tobst/radmesserS/images/device/device_case_2.jpg

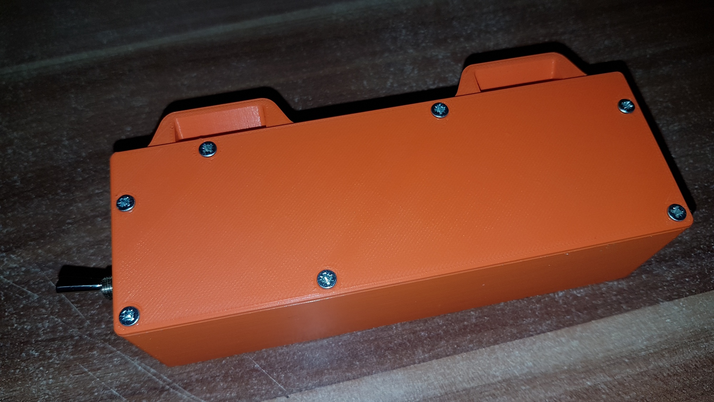
images/device/device_case_2.jpg
