tobst/radmesserS/images/device/device_case_3.jpg

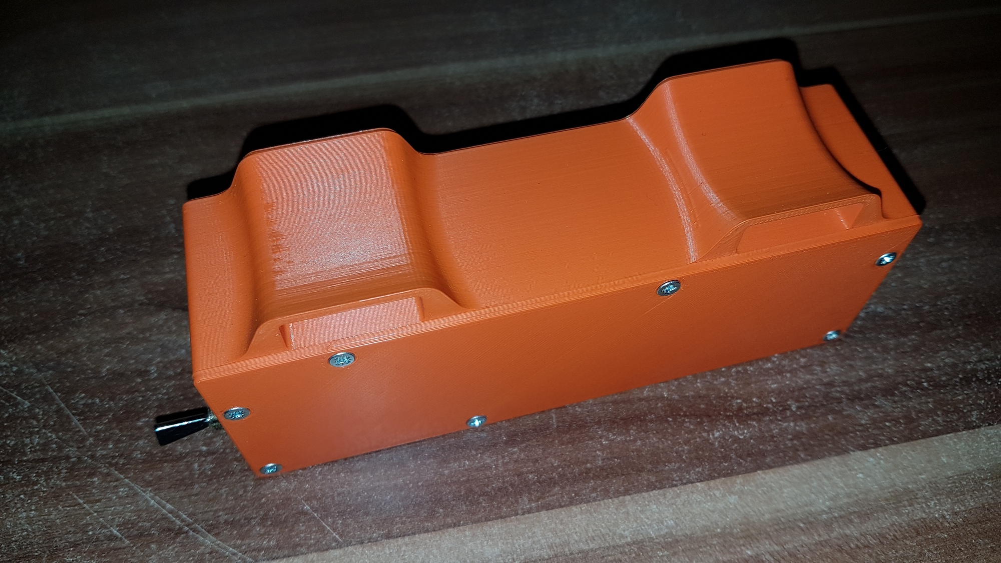
images/device/device_case_3.jpg
