tobst/radmesserS/images/device/device_case_4.jpg

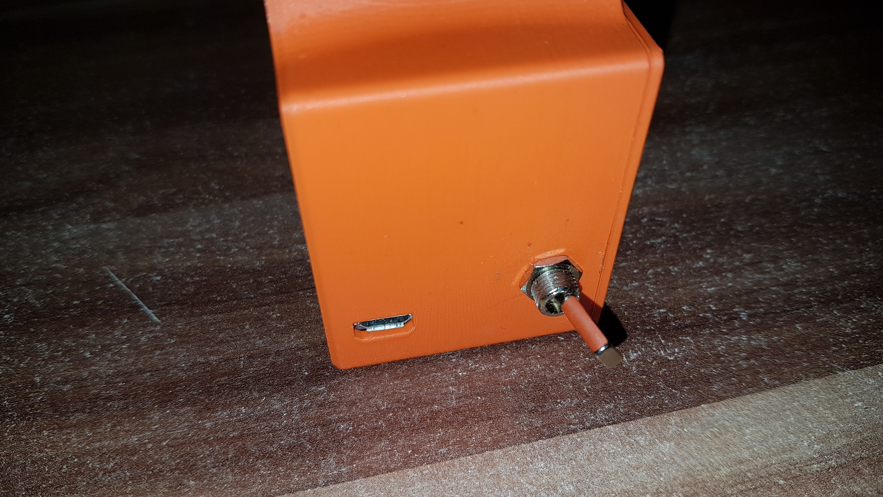
images/device/device_case_4.jpg
