tobst/radmesserS/images/device/device_internals.jpg

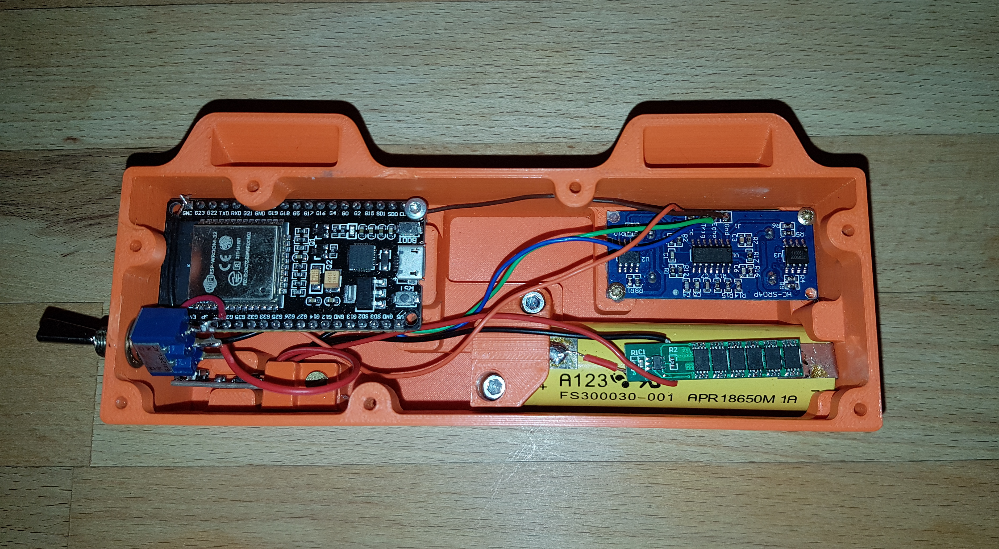
images/device/device_internals.jpg
