tobst/radmesserS/images/device/radmessers-fritzing.png

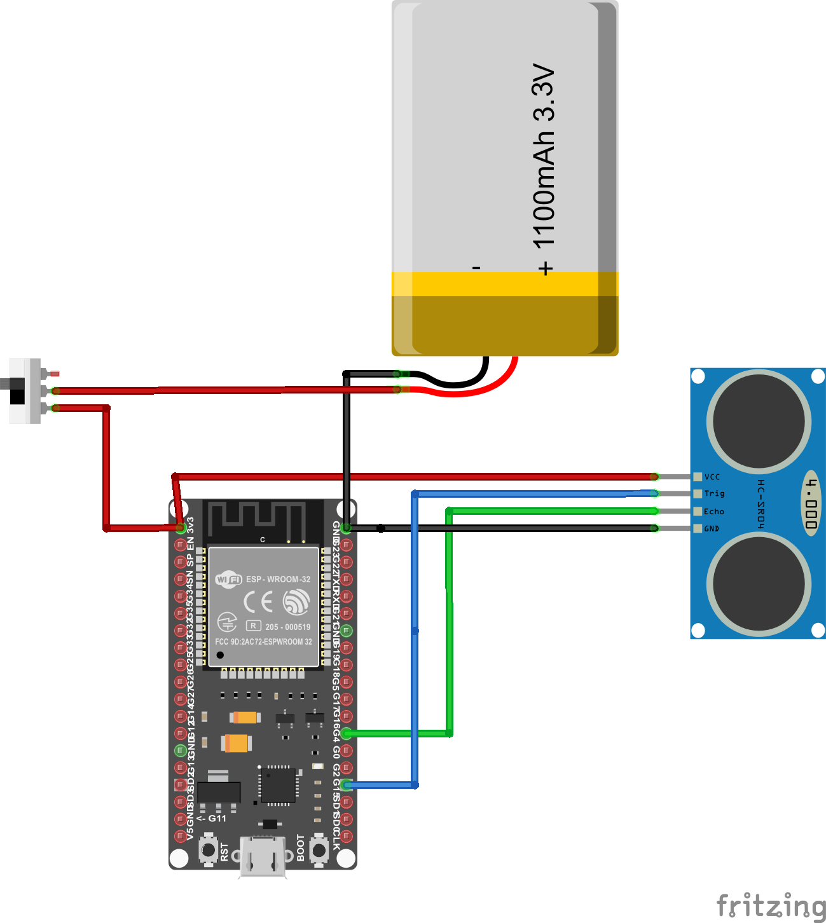
images/device/radmessers-fritzing.png
