tobst/radmesserS/images/device/TP5000-Charger-and-LiFePo-Protection-Board.jpg

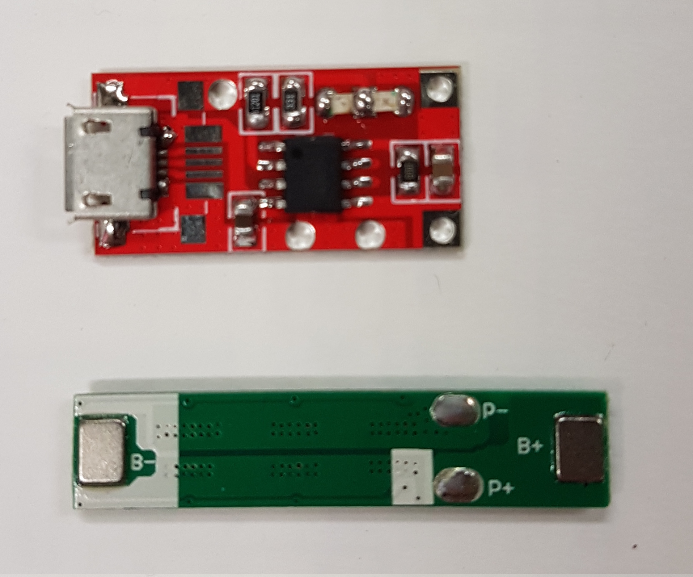
images/device/TP5000-Charger-and-LiFePo-Protection-Board.jpg
