tobst/radmesserS/images/mounting_0.jpg

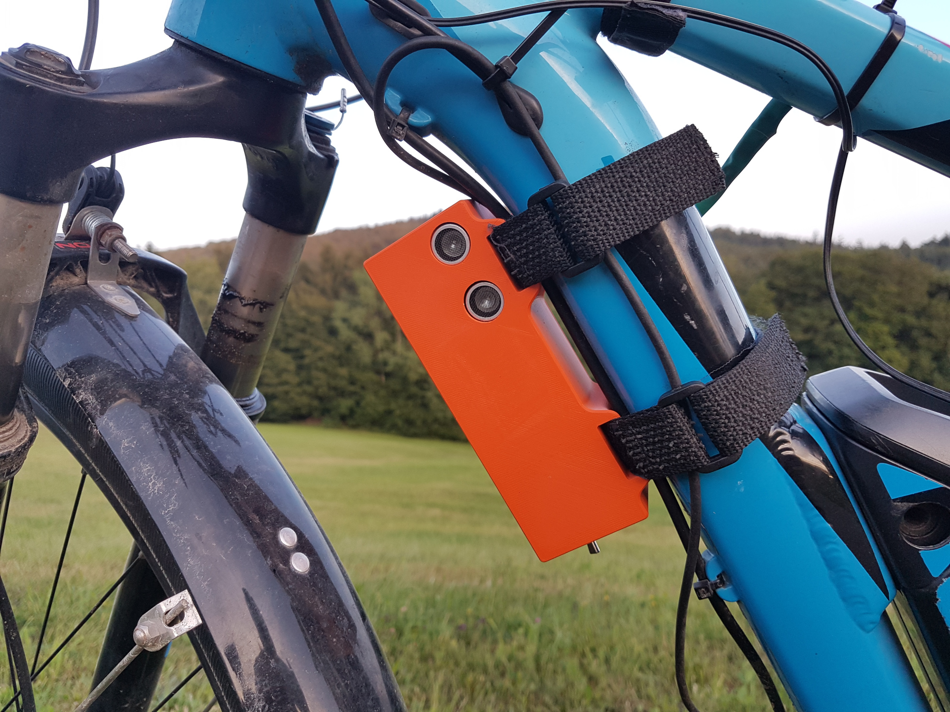
images/mounting_0.jpg
