tobst/radmesserS/images/screenshots/blescanner/ble_scanner_1.jpg

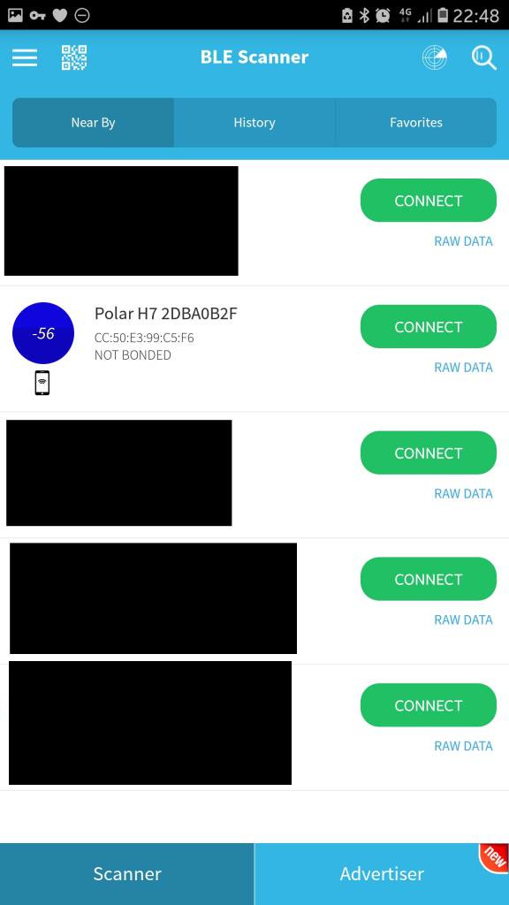
images/screenshots/blescanner/ble_scanner_1.jpg
