tobst/radmesserS/images/screenshots/blescanner/ble_scanner_2.jpg

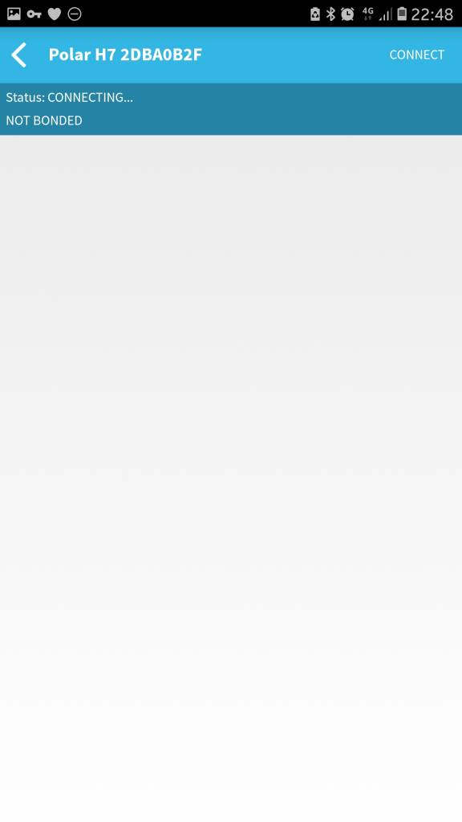
images/screenshots/blescanner/ble_scanner_2.jpg
