tobst/radmesserS/images/screenshots/blescanner/ble_scanner_2_800x800.jpg

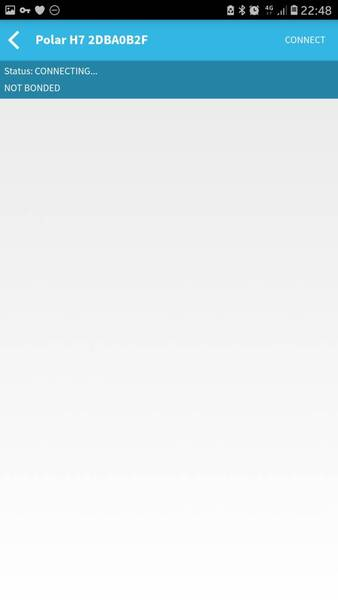
images/screenshots/blescanner/ble_scanner_2_800x800.jpg
