tobst/radmesserS/images/screenshots/blescanner/ble_scanner_3.jpg

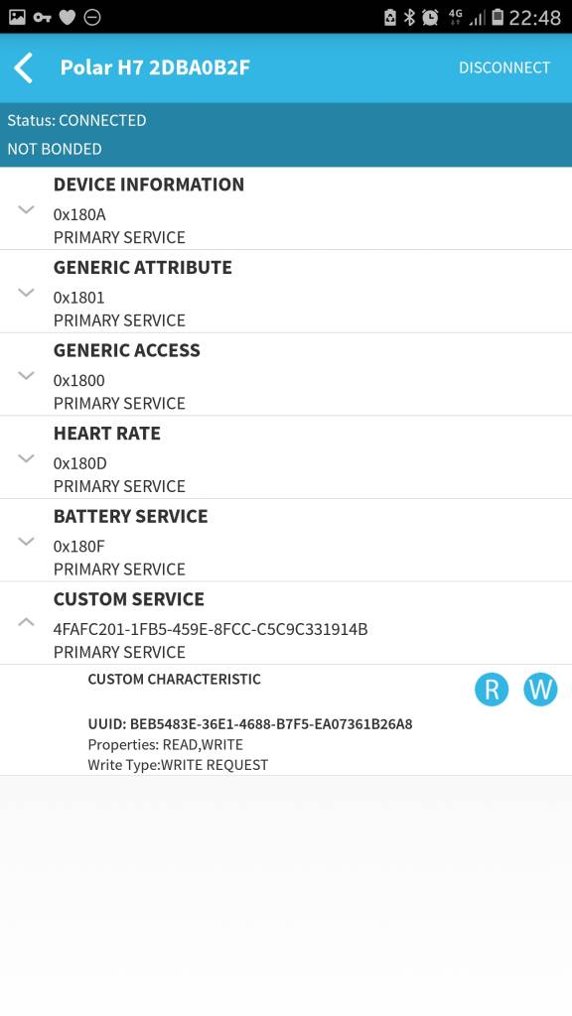
images/screenshots/blescanner/ble_scanner_3.jpg
