tobst/radmesserS/images/screenshots/blescanner/ble_scanner_4.jpg

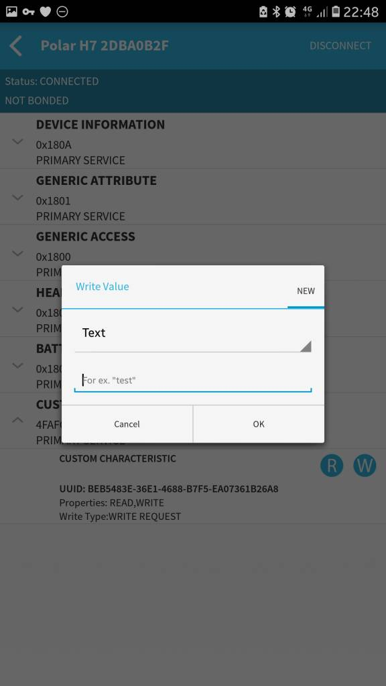
images/screenshots/blescanner/ble_scanner_4.jpg
