tobst/radmesserS/images/screenshots/runnerup/export/runnerup_export_to_directory_1.jpg

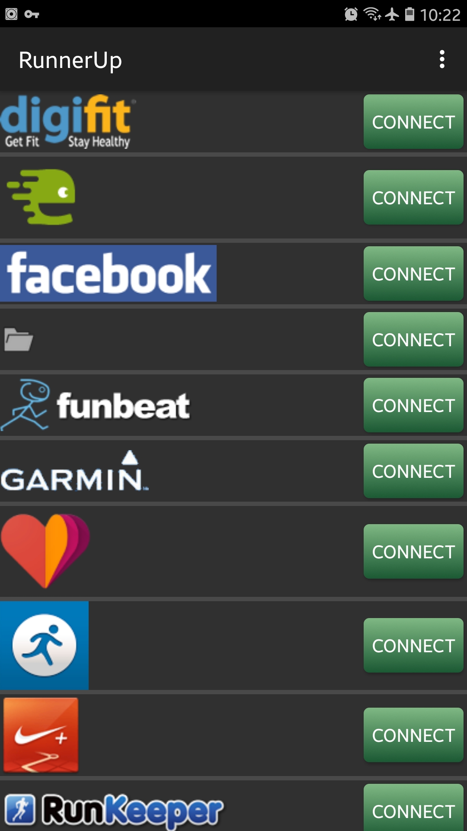
images/screenshots/runnerup/export/runnerup_export_to_directory_1.jpg
