tobst/radmesserS/images/screenshots/runnerup/export/runnerup_export_to_directory_2.jpg

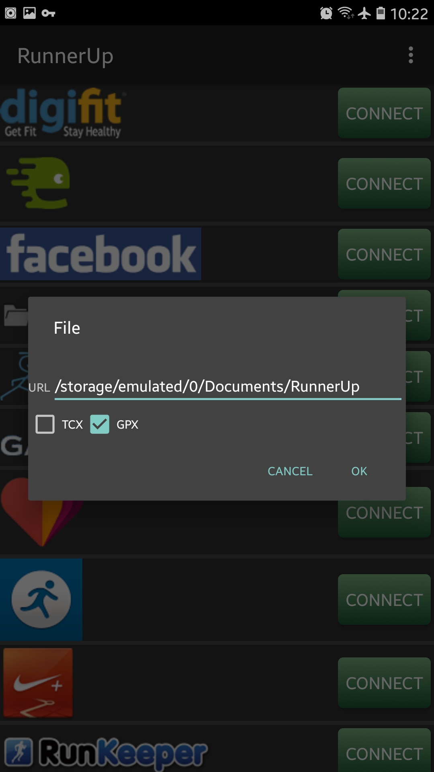
images/screenshots/runnerup/export/runnerup_export_to_directory_2.jpg
