tobst/radmesserS/images/screenshots/runnerup/runnerup_1.jpg

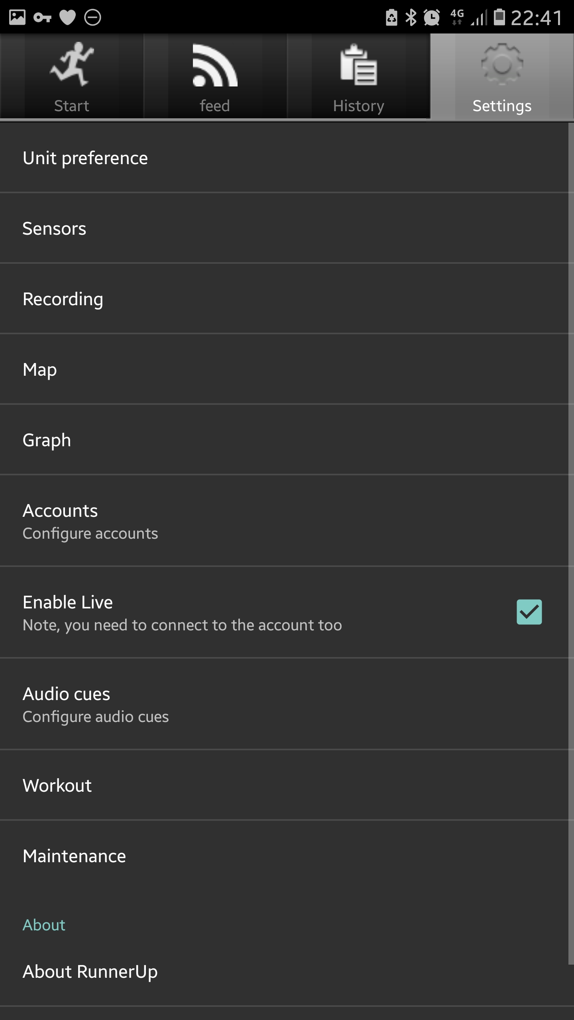
images/screenshots/runnerup/runnerup_1.jpg
