tobst/radmesserS/images/screenshots/runnerup/runnerup_2.jpg

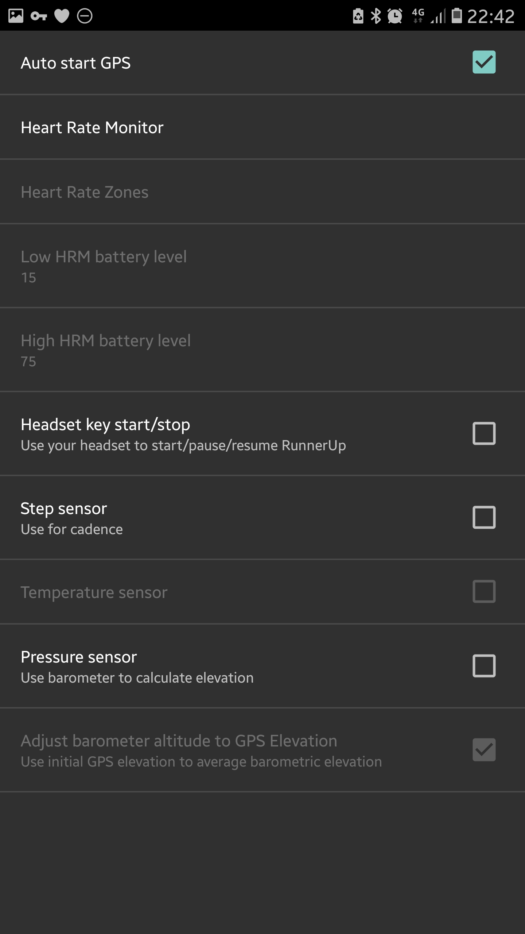
images/screenshots/runnerup/runnerup_2.jpg
