tobst/radmesserS/images/screenshots/runnerup/runnerup_3.jpg

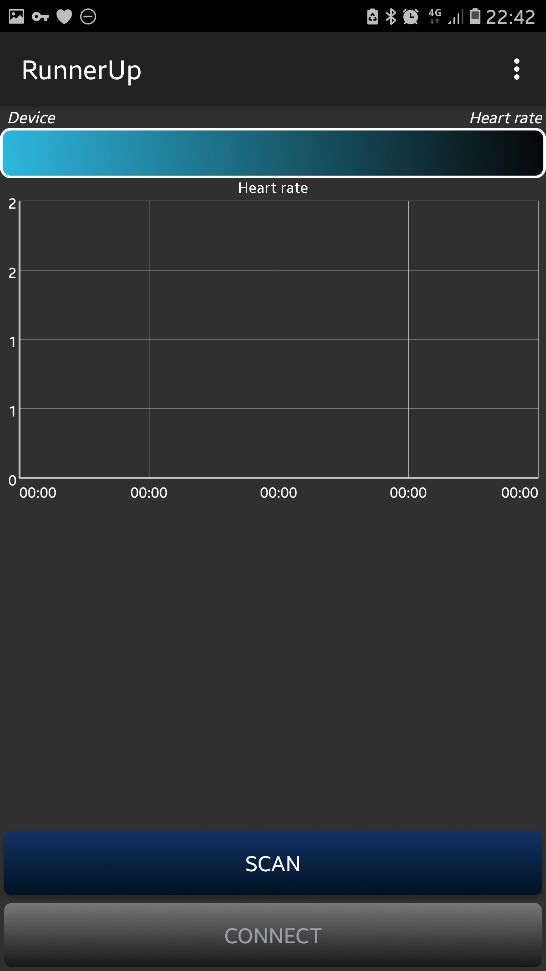
images/screenshots/runnerup/runnerup_3.jpg
