tobst/radmesserS/images/screenshots/runnerup/runnerup_4.jpg

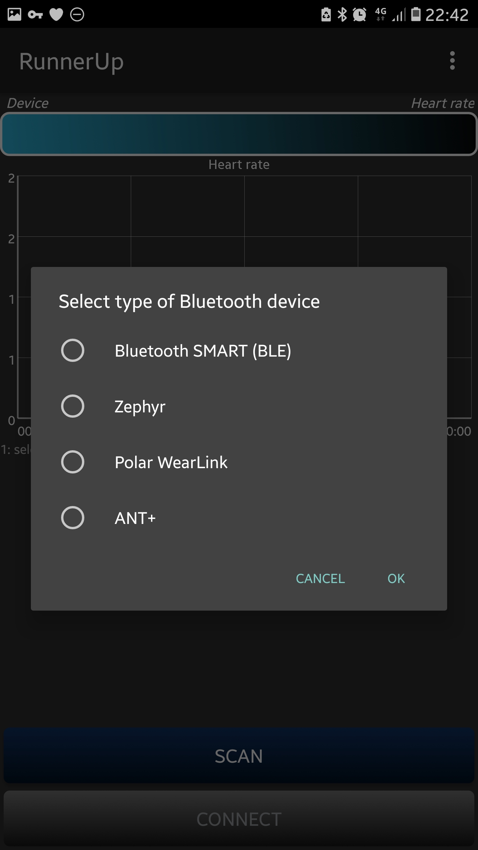
images/screenshots/runnerup/runnerup_4.jpg
