tobst/radmesserS/images/screenshots/runnerup/runnerup_6.jpg

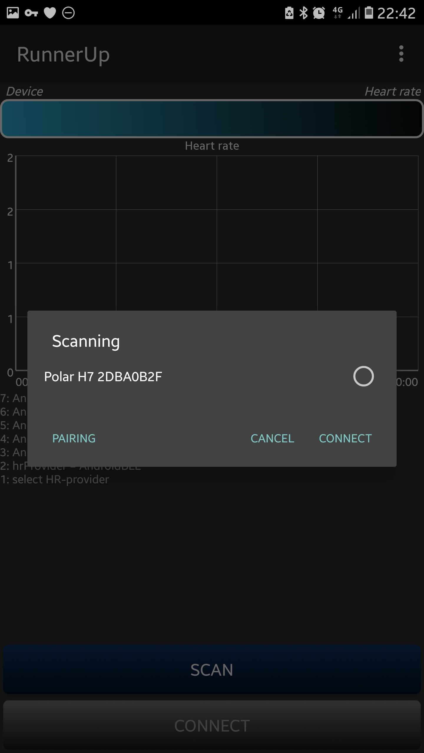
images/screenshots/runnerup/runnerup_6.jpg
