tobst/radmesserS/images/screenshots/runnerup/runnerup_8.jpg

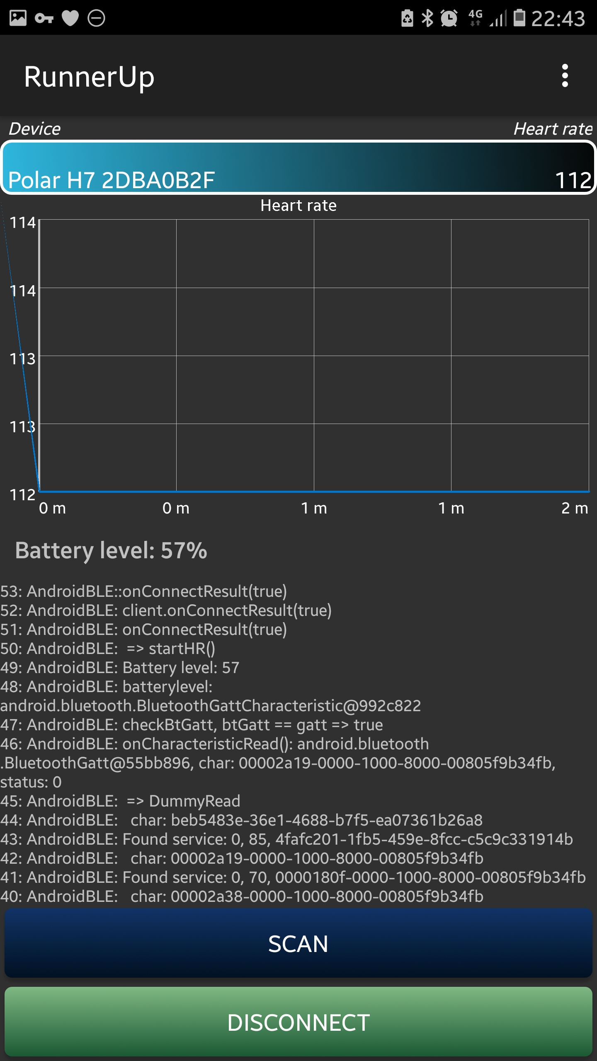
images/screenshots/runnerup/runnerup_8.jpg
