tobst/radmesserS/images/screenshots/runnerup/runnerup_9.jpg

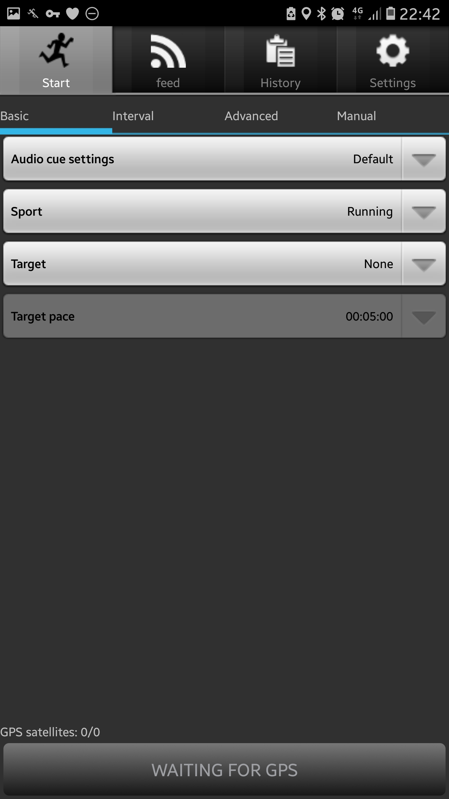
images/screenshots/runnerup/runnerup_9.jpg
