tobst/radmesserS/images/screenshots/runnerup/runnerup_10.jpg

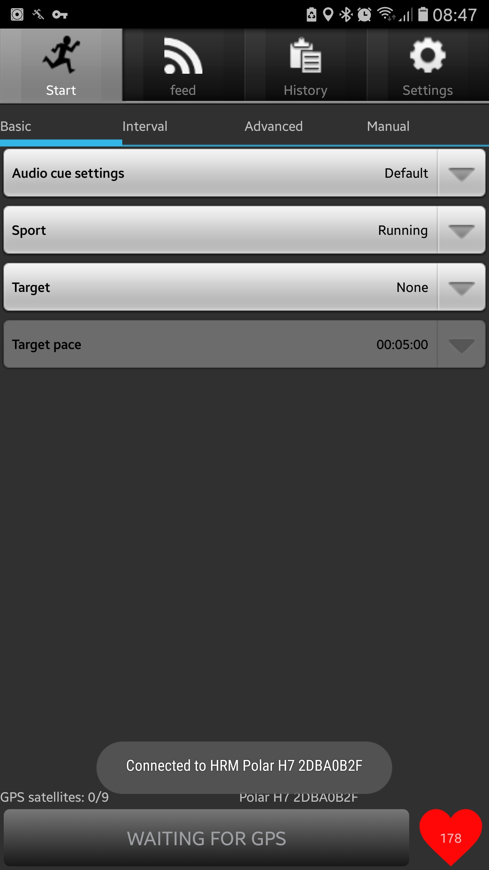
images/screenshots/runnerup/runnerup_10.jpg
