tobst/radmesserS/Pictures/radmesserS-Fritzing_ProtectionBoard.png

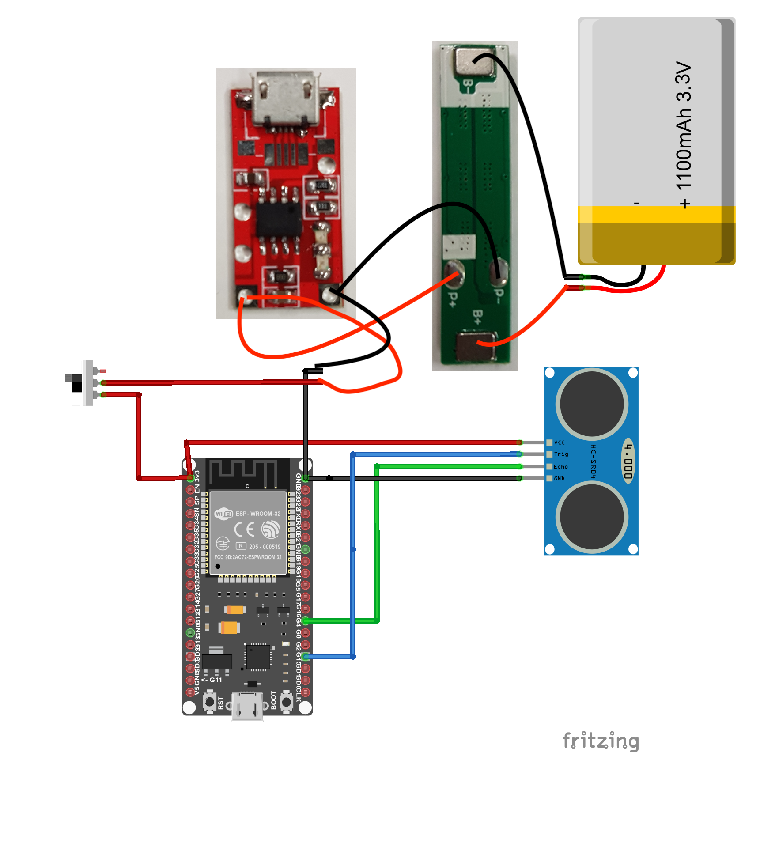
Pictures/radmesserS-Fritzing_ProtectionBoard.png
