tobst/radmesserS/BLE_DISTANCE_SENSOR_V2/gps.ino

void readGPSData() {
  gpsState.distMax = 0;
  gpsState.altMax = -999999;
  gpsState.spdMax = 0;
  gpsState.altMin = 999999;

  while (SerialGPS.available() > 0) {
    gps.encode(SerialGPS.read());
  }
  Serial.print(F("DIAGS      Chars="));
  Serial.print(gps.charsProcessed());
  Serial.print(F(" Sentences-with-Fix="));
  Serial.print(gps.sentencesWithFix());
  Serial.print(F(" Failed-checksum="));
  Serial.print(gps.failedChecksum());
  Serial.print(F(" Passed-checksum="));
  Serial.println(gps.passedChecksum());

  if (gps.satellites.value() > 4) {
    gpsState.dist = TinyGPSPlus::distanceBetween(gps.location.lat(), gps.location.lng(), gpsState.originLat, gpsState.originLon);

    if (gpsState.dist > gpsState.distMax && abs(gpsState.prevDist - gpsState.dist) < 50) {
      gpsState.distMax = gpsState.dist;
    }
    gpsState.prevDist = gpsState.dist;

    if (gps.altitude.meters() > gpsState.altMax) {
      gpsState.altMax = gps.altitude.meters();
    }

    if (gps.speed.kmph() > gpsState.spdMax) {
      gpsState.spdMax = gps.speed.kmph();
    }

    if (gps.altitude.meters() < gpsState.altMin) {
      gpsState.altMin = gps.altitude.meters();
    }
  }
  if (nextSerialTaskTs < millis()) {
    Serial.print("LAT=");  Serial.println(gps.location.lat(), 6);
    Serial.print("LONG="); Serial.println(gps.location.lng(), 6);
    Serial.print("ALT=");  Serial.println(gps.altitude.meters());
    Serial.print("Sats=");  Serial.println(gps.satellites.value());
    Serial.print("DST: ");
    Serial.println(gpsState.dist, 1);
    nextSerialTaskTs = millis() + TASK_SERIAL_RATE;
  }

}

void writeLastFixToEEPROM() {
  // Aktuelle Position in nichtflüchtigen ESP32-Speicher schreiben
  long writeValue;
  writeValue = gpsState.originLat * 1000000;
  EEPROM_writeAnything(4, writeValue);
  writeValue = gpsState.originLon * 1000000;
  EEPROM_writeAnything(8, writeValue);
  writeValue = gpsState.originAlt * 1000000;
  EEPROM_writeAnything(12, writeValue);
  EEPROM.commit(); // erst mit commit() werden die Daten geschrieben
}

void readLastFixFromEEPROM() {
  /*
    Read last gps fix from EEPROM
  */
  long readValue;
  EEPROM_readAnything(4, readValue);
  gpsState.originLat = (double)readValue / 1000000;

  EEPROM_readAnything(8, readValue);
  gpsState.originLon = (double)readValue / 1000000;

  EEPROM_readAnything(12, readValue);
  gpsState.originAlt = (double)readValue / 1000000;
}
