tobst/radmesserS/BLE_DISTANCE_SENSOR_V2/gps.h

#include <TinyGPS++.h> // Library über http://arduiniana.org/libraries/tinygpsplus/ downloaden und installieren
#include <HardwareSerial.h> // sollte bereits mit Arduino IDE installiert sein

//GPS
TinyGPSPlus gps;
HardwareSerial SerialGPS(1);
struct GpsDataState_t {
  double originLat = 0;
  double originLon = 0;
  double originAlt = 0;
  double distMax = 0;
  double dist = 0;
  double altMax = -999999;
  double altMin = 999999;
  double spdMax = 0;
  double prevDist = 0;
};
GpsDataState_t gpsState = {};
